curiouselectric/TVBGone/TVBGone_Hardware/TVBGone_KiCAD/TV_B_Gone_ML_v1_2.sch

## KiCad design TVBGone_Hardware/TVBGone_KiCAD/TV_B_Gone_ML_v1_2.sch (2018-12-30, an earlier design)

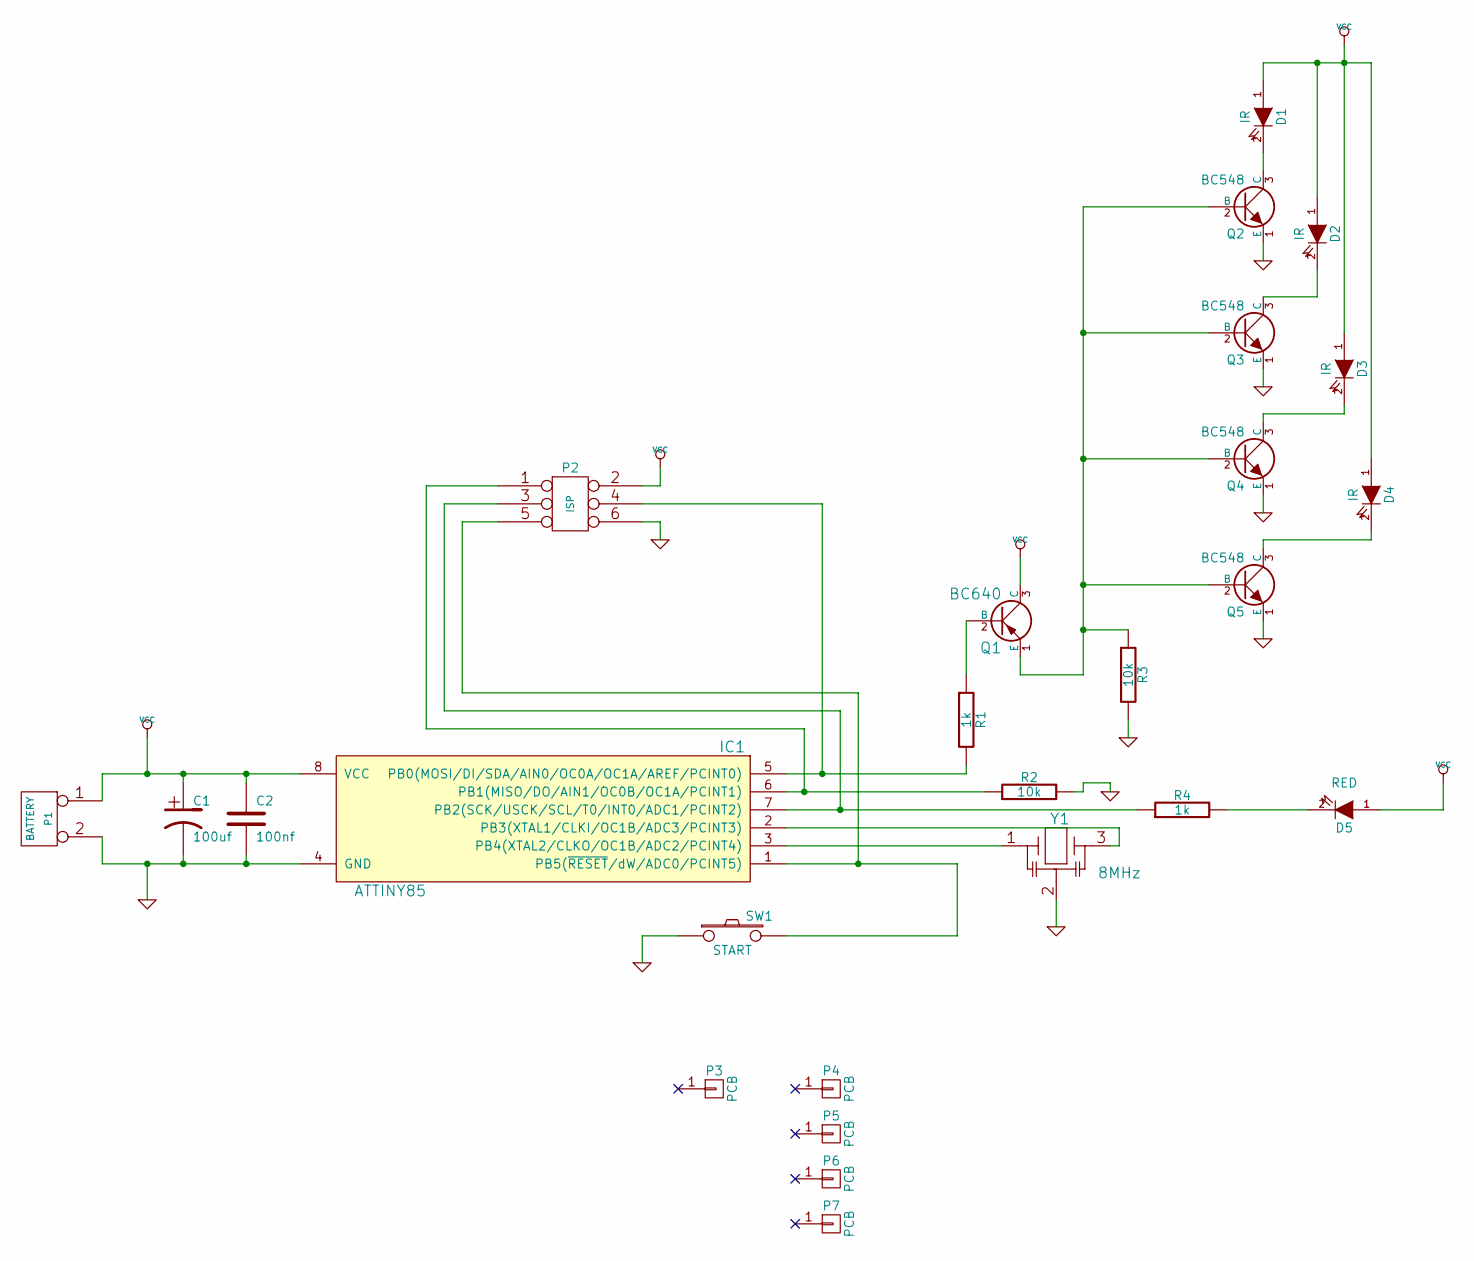
[picture p34: schematic TV_B_Gone_ML_v1_2.sch]

Parts:
C1: 100uf; C1V7_lg_pad
C2: 100nf; C1_wide_lg_pad
D1, D2, D3, D4: IR; LED-5MM_larg_pad
D5: RED; LED-5MM_larg_pad
IC1: ATTINY85; DIP-8__300_ELL
P1: BATTERY; conn_2_battery
P2: ISP; TH3x2_ISP
P3: PCB; dp_devices-DP5031_V1
P4, P5, P6, P7: PCB; NPTH_3MM
Q1: BC640; TO92-ECB_large_pad_BC639
Q2, Q3, Q4, Q5: BC548; TO92-EBC_large_pad
R1, R4: 1k; TH_Resistor_1
R2, R3: 10k; TH_Resistor_1
SW1: START; SW_PUSH_SMALL_lg_pad
Y1: 8MHz; SIL-3_lg_pad

Connections:
GND: C1.2, C2.2, IC1.4 (GND), P1.2, P2.6, Q2.1 (E), Q3.1 (E), Q4.1 (E), Q5.1 (E), R2.2, R3.2, SW1.1, Y1.2
unnamed: D1.2 (K), Q2.3 (C)
unnamed: D2.2 (K), Q3.3 (C)
unnamed: D3.2 (K), Q4.3 (C)
unnamed: D4.2 (K), Q5.3 (C)
unnamed: D5.2 (K), R4.2
unnamed: IC1.1 (PB5(~RESET~/dW/ADC0/PCINT5)), P2.5, SW1.2
unnamed: IC1.2 (PB3(XTAL1/CLKI/OC1B/ADC3/PCINT3)), Y1.3
unnamed: IC1.3 (PB4(XTAL2/CLKO/OC1B/ADC2/PCINT4)), Y1.1
unnamed: IC1.5 (PB0(MOSI/DI/SDA/AIN0/OC0A/OC1A/AREF/PCI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), P2.4, R1.2
unnamed: IC1.6 (PB1(MISO/DO/AIN1/OC0B/OC1A/PCINT1)), P2.1, R2.1
unnamed: IC1.7 (PB2(SCK/USCK/SCL/T0/INT0/ADC1/PCINT2)), P2.3, R4.1
unnamed: Q1.1 (E), Q2.2 (B), Q3.2 (B), Q4.2 (B), Q5.2 (B), R3.1
unnamed: Q1.2 (B), R1.1
VCC: C1.1, C2.1, D1.1 (A), D2.1 (A), D3.1 (A), D4.1 (A), D5.1 (A), IC1.8 (VCC), P1.1, P2.2, Q1.3 (C)
